erkannt/neuro36/artwork/36.png

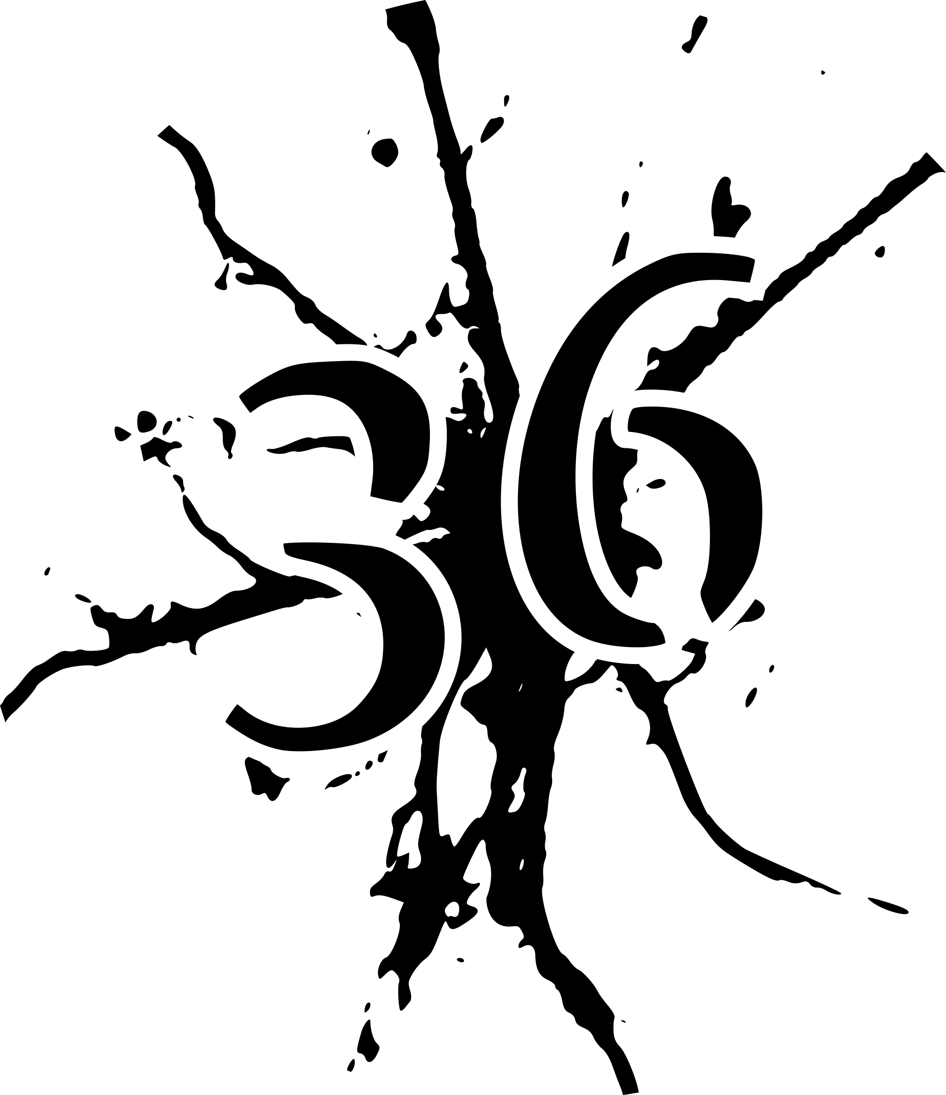
artwork/36.png
