erkannt/neuro36/rknt36.kicad_sch

## KiCad design rknt36.kicad_sch (2023-09-02)

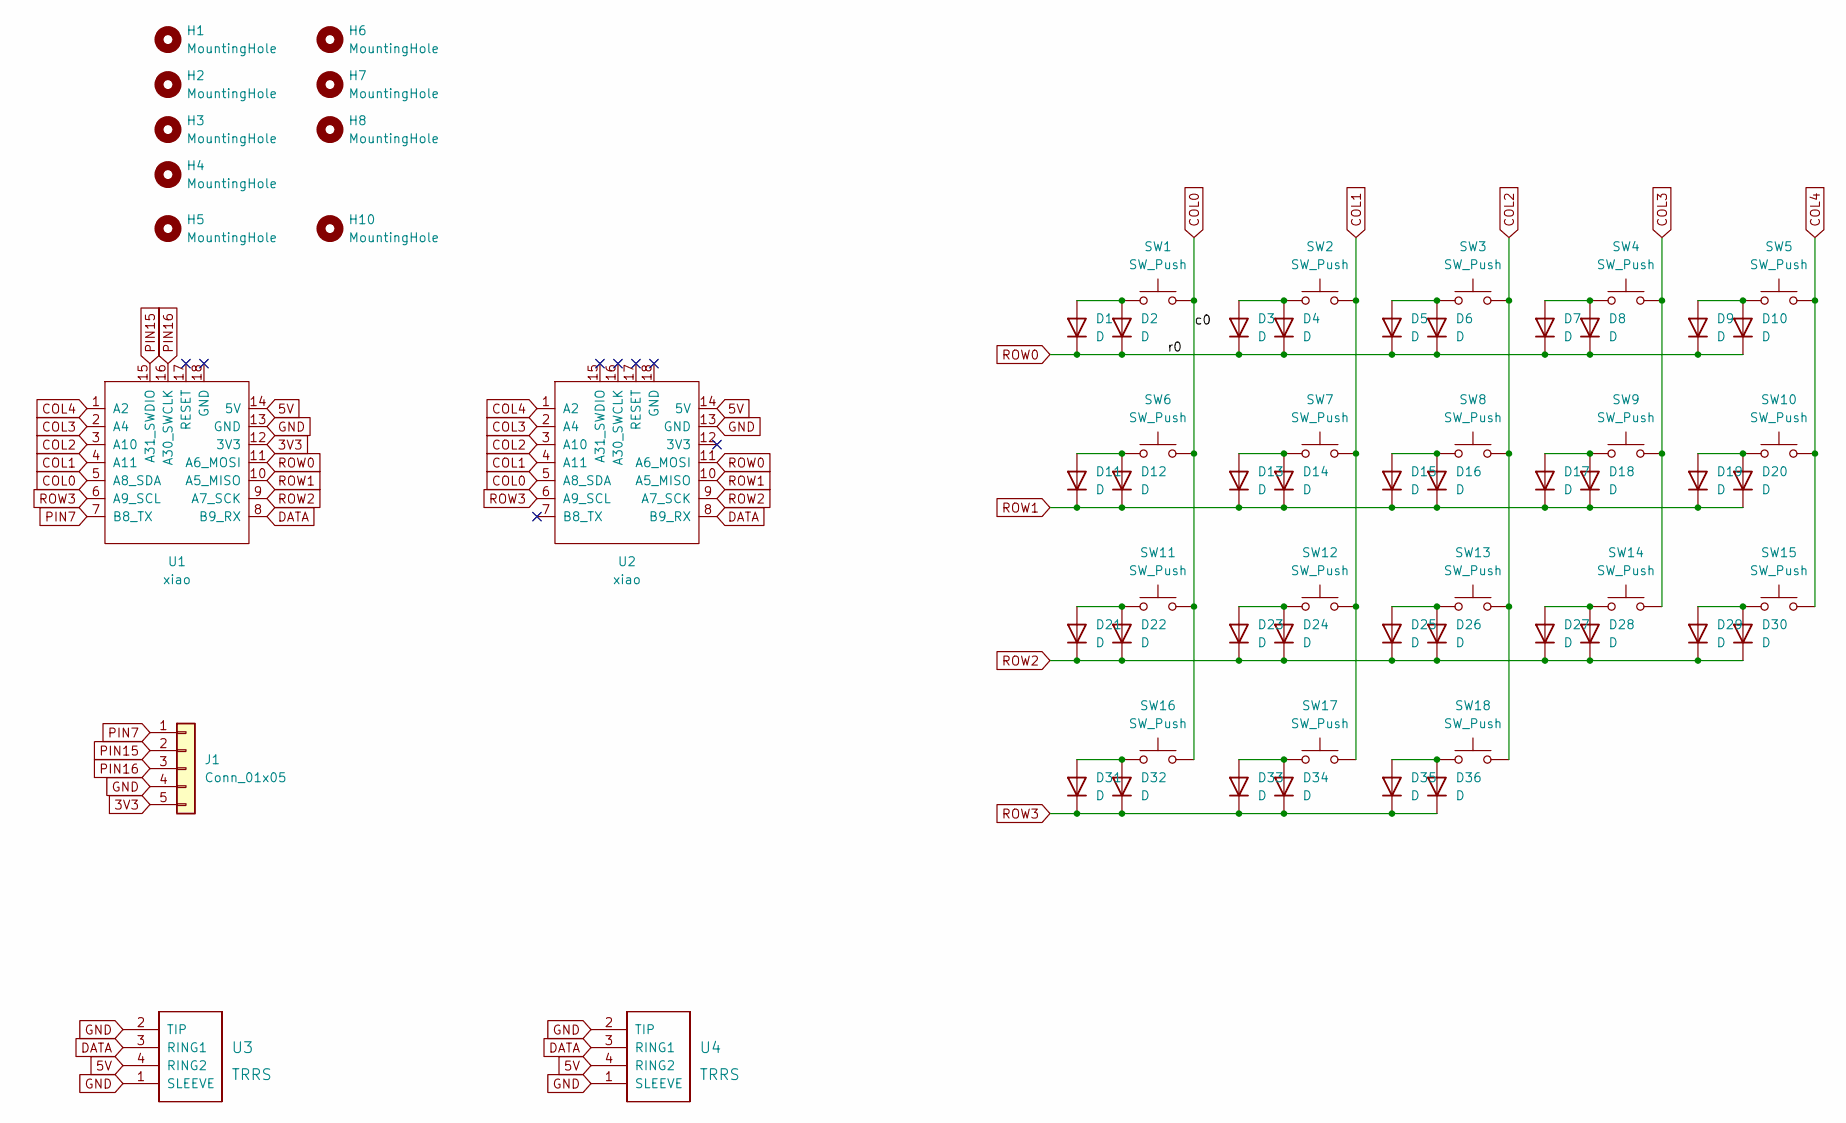
[picture p13: schematic rknt36.kicad_sch]

Parts:
D1, D2, D3, D4, D5, D6, D7, D8, D9, D10, D11, D12, D13, D14, D15, D16, D17, D18, D19, D20, D21, D22, D23, D24, D25, D26, D27, D28, D29, D30, D31, D32, D33, D34, D35, D36: D; 0805_diode
H1, H2, H3, H4, H5, H6, H7, H8, H10: MountingHole; MountingHole_2.2mm_M2_DIN965_Pad
J1: Conn_01x05; PinHeader_1x05_P2.54mm_Vertical
SW1, SW2, SW3, SW4, SW5, SW6, SW7, SW8, SW9, SW10, SW11, SW12, SW13, SW14, SW15: SW_Push; Kailh_socket_PG1350_optional_reversible
SW16, SW17, SW18: SW_Push; SW_PG1350_reversible_rotatable
U1, U2: xiao; xiao-smd
U3, U4: TRRS; TRRS-PJ-320A

Connections:
3V3: J1.5, U1.12 (3V3)
5V: U1.14 (5V), U2.14 (5V), U3.4 (RING2), U4.4 (RING2)
COL0: SW1.2, SW6.2, SW11.2, SW16.2, U1.5 (A8_SDA), U2.5 (A8_SDA)
COL1: SW2.2, SW7.2, SW12.2, SW17.2, U1.4 (A11), U2.4 (A11)
COL2: SW3.2, SW8.2, SW13.2, SW18.2, U1.3 (A10), U2.3 (A10)
COL3: SW4.2, SW9.2, SW14.2, U1.2 (A4), U2.2 (A4)
COL4: SW5.2, SW10.2, SW15.2, U1.1 (A2), U2.1 (A2)
DATA: U1.8 (B9_RX), U2.8 (B9_RX), U3.3 (RING1), U4.3 (RING1)
GND: J1.4, U1.13 (GND), U2.13 (GND), U3.1 (SLEEVE), U3.2 (TIP), U4.1 (SLEEVE), U4.2 (TIP)
unnamed: D1.2 (A), D2.2 (A), SW1.1
unnamed: D3.2 (A), D4.2 (A), SW2.1
unnamed: D5.2 (A), D6.2 (A), SW3.1
unnamed: D7.2 (A), D8.2 (A), SW4.1
unnamed: D9.2 (A), D10.2 (A), SW5.1
unnamed: D11.2 (A), D12.2 (A), SW6.1
unnamed: D13.2 (A), D14.2 (A), SW7.1
unnamed: D15.2 (A), D16.2 (A), SW8.1
unnamed: D17.2 (A), D18.2 (A), SW9.1
unnamed: D19.2 (A), D20.2 (A), SW10.1
unnamed: D21.2 (A), D22.2 (A), SW11.1
unnamed: D23.2 (A), D24.2 (A), SW12.1
unnamed: D25.2 (A), D26.2 (A), SW13.1
unnamed: D27.2 (A), D28.2 (A), SW14.1
unnamed: D29.2 (A), D30.2 (A), SW15.1
unnamed: D31.2 (A), D32.2 (A), SW16.1
unnamed: D33.2 (A), D34.2 (A), SW17.1
unnamed: D35.2 (A), D36.2 (A), SW18.1
PIN7: J1.1, U1.7 (B8_TX)
PIN15: J1.2, U1.15 (A31_SWDIO)
PIN16: J1.3, U1.16 (A30_SWCLK)
ROW0: D1.1 (K), D2.1 (K), D3.1 (K), D4.1 (K), D5.1 (K), D6.1 (K), D7.1 (K), D8.1 (K), D9.1 (K), D10.1 (K), U1.11 (A6_MOSI), U2.11 (A6_MOSI)
ROW1: D11.1 (K), D12.1 (K), D13.1 (K), D14.1 (K), D15.1 (K), D16.1 (K), D17.1 (K), D18.1 (K), D19.1 (K), D20.1 (K), U1.10 (A5_MISO), U2.10 (A5_MISO)
ROW2: D21.1 (K), D22.1 (K), D23.1 (K), D24.1 (K), D25.1 (K), D26.1 (K), D27.1 (K), D28.1 (K), D29.1 (K), D30.1 (K), U1.9 (A7_SCK), U2.9 (A7_SCK)
ROW3: D31.1 (K), D32.1 (K), D33.1 (K), D34.1 (K), D35.1 (K), D36.1 (K), U1.6 (A9_SCL), U2.6 (A9_SCL)
